xiaokaizip/debugger/README.assets/image-20221211133038720.png

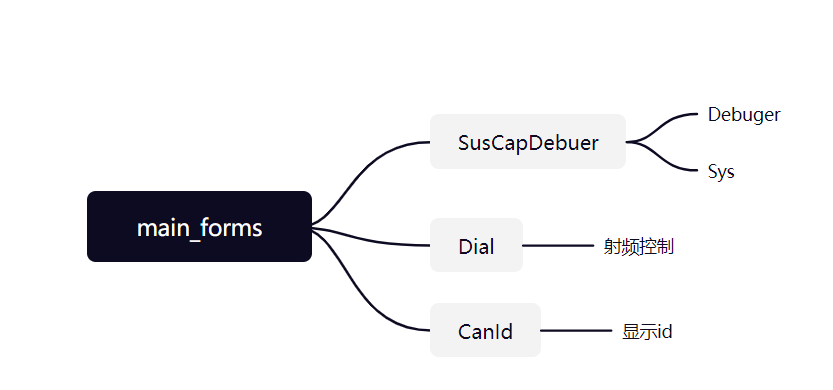
README.assets/image-20221211133038720.png
