xiaokaizip/debugger/debugger_code_f407/forms/motor_forms.h

//
// Created by 86136 on 2023/3/27.
//

#ifndef DEBUGGER_CODE_MOTOR_FORMS_H
#define DEBUGGER_CODE_MOTOR_FORMS_H

void Motor_Form_Init();

void Motor_Form_Load();

#endif //DEBUGGER_CODE_MOTOR_FORMS_H
