xiaokaizip/debugger/debugger_code_f103/hardwares/usart.c

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
/* Includes ------------------------------------------------------------------*/
#include "usart.h"

/* USER CODE BEGIN 0 */
#include "string.h"
#include "retarget.h"

extern uint16_t usart_times;
extern char usart_name[20];
extern uint8_t usart_data[8];

//串口中断的回调函数
void HAL_UART_RxCpltCallback(UART_HandleTypeDef *huart) {
    if (huart == &huart1) {
        strcpy(usart_name, "usart_typeC");
        usart_times = 0;
    } else if (huart == &huart4) {
        strcpy(usart_name, "usart_gh1.25");
        usart_times = 0;
    }
    HAL_UART_Receive_IT(&huart1, usart_data, 8);
    HAL_UART_Receive_IT(&huart4, usart_data, 8);
}

/* USER CODE END 0 */

UART_HandleTypeDef huart4;
UART_HandleTypeDef huart1;

/* UART4 init function */
void MX_UART4_Init(void) {

    huart4.Instance = UART4;
    huart4.Init.BaudRate = 115200;
    huart4.Init.WordLength = UART_WORDLENGTH_8B;
    huart4.Init.StopBits = UART_STOPBITS_1;
    huart4.Init.Parity = UART_PARITY_NONE;
    huart4.Init.Mode = UART_MODE_TX_RX;
    huart4.Init.HwFlowCtl = UART_HWCONTROL_NONE;
    huart4.Init.OverSampling = UART_OVERSAMPLING_16;
    if (HAL_UART_Init(&huart4) != HAL_OK) {
        Error_Handler();
    }
}

/* USART1 init function */

void MX_USART1_UART_Init(void) {

    huart1.Instance = USART1;
    huart1.Init.BaudRate = 115200;
    huart1.Init.WordLength = UART_WORDLENGTH_8B;
    huart1.Init.StopBits = UART_STOPBITS_1;
    huart1.Init.Parity = UART_PARITY_NONE;
    huart1.Init.Mode = UART_MODE_TX_RX;
    huart1.Init.HwFlowCtl = UART_HWCONTROL_NONE;
    huart1.Init.OverSampling = UART_OVERSAMPLING_16;
    if (HAL_UART_Init(&huart1) != HAL_OK) {
        Error_Handler();
    }
}

void HAL_UART_MspInit(UART_HandleTypeDef *uartHandle) {

    GPIO_InitTypeDef GPIO_InitStruct = {0};
    if (uartHandle->Instance == UART4) {
        /* UART4 clock enable */
        __HAL_RCC_UART4_CLK_ENABLE();

        __HAL_RCC_GPIOC_CLK_ENABLE();
        /**UART4 GPIO Configuration
        PC10     ------> UART4_TX
        PC11     ------> UART4_RX
        */
        GPIO_InitStruct.Pin = GPIO_PIN_10;
        GPIO_InitStruct.Mode = GPIO_MODE_AF_PP;
        GPIO_InitStruct.Speed = GPIO_SPEED_FREQ_HIGH;
        HAL_GPIO_Init(GPIOC, &GPIO_InitStruct);

        GPIO_InitStruct.Pin = GPIO_PIN_11;
        GPIO_InitStruct.Mode = GPIO_MODE_INPUT;
        GPIO_InitStruct.Pull = GPIO_NOPULL;
        HAL_GPIO_Init(GPIOC, &GPIO_InitStruct);

        /* UART4 interrupt Init */
        HAL_NVIC_SetPriority(UART4_IRQn, 0, 0);
        HAL_NVIC_EnableIRQ(UART4_IRQn);
    } else if (uartHandle->Instance == USART1) {
        /* USART1 clock enable */
        __HAL_RCC_USART1_CLK_ENABLE();

        __HAL_RCC_GPIOA_CLK_ENABLE();
        /**USART1 GPIO Configuration
        PA9     ------> USART1_TX
        PA10     ------> USART1_RX
        */
        GPIO_InitStruct.Pin = GPIO_PIN_9;
        GPIO_InitStruct.Mode = GPIO_MODE_AF_PP;
        GPIO_InitStruct.Speed = GPIO_SPEED_FREQ_HIGH;
        HAL_GPIO_Init(GPIOA, &GPIO_InitStruct);

        GPIO_InitStruct.Pin = GPIO_PIN_10;
        GPIO_InitStruct.Mode = GPIO_MODE_INPUT;
        GPIO_InitStruct.Pull = GPIO_NOPULL;
        HAL_GPIO_Init(GPIOA, &GPIO_InitStruct);

        /* USART1 interrupt Init */
        HAL_NVIC_SetPriority(USART1_IRQn, 0, 0);
        HAL_NVIC_EnableIRQ(USART1_IRQn);
    }
}

void HAL_UART_MspDeInit(UART_HandleTypeDef *uartHandle) {

    if (uartHandle->Instance == UART4) {
        /* Peripheral clock disable */
        __HAL_RCC_UART4_CLK_DISABLE();

        /**UART4 GPIO Configuration
        PC10     ------> UART4_TX
        PC11     ------> UART4_RX
        */
        HAL_GPIO_DeInit(GPIOC, GPIO_PIN_10 | GPIO_PIN_11);

        /* UART4 interrupt Deinit */
        HAL_NVIC_DisableIRQ(UART4_IRQn);
    } else if (uartHandle->Instance == USART1) {
        /* Peripheral clock disable */
        __HAL_RCC_USART1_CLK_DISABLE();

        /**USART1 GPIO Configuration
        PA9     ------> USART1_TX
        PA10     ------> USART1_RX
        */
        HAL_GPIO_DeInit(GPIOA, GPIO_PIN_9 | GPIO_PIN_10);

        /* USART1 interrupt Deinit */
        HAL_NVIC_DisableIRQ(USART1_IRQn);
    }
}
