xiaokaizip/debugger/debugger_code_f103/system/system.h

//
// Created by 86136 on 2023/1/15.
//

#ifndef DEBUGGER_CODE_SYSTEM_H
#define DEBUGGER_CODE_SYSTEM_H

unsigned short FloatToInt16(float data0);

float Int16ToFloat(unsigned short data0);

#endif //DEBUGGER_CODE_SYSTEM_H
