xiaokaizip/debugger/debugger_code_f407/function/led.c

/*

The MIT License (MIT)

Copyright (c) 2016 Hubert Denkmair

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
*/

#include "led.h"
#include <string.h>
#include "main.h"

#define SEQ_ISPASSED(now, target) ((int32_t) ((now) - (target)) >= 0)   /*判断大小*/

/**
 * 初始化led灯
 * @param leds led的结构体
 * @param led1_port LED1引脚所在的组
 * @param led1_pin  LED1的引脚号
 * @param led1_active_high
 * @param led2_port LED2引脚所在的组
 * @param led2_pin  LED2的引脚号
 * @param led2_active_high
 */
void led_init(
        led_data_t *leds,
        void *led1_port, uint16_t led1_pin, bool led1_active_high,
        void *led2_port, uint16_t led2_pin, bool led2_active_high
) {
    memset(leds, 0, sizeof(led_data_t));
    leds->led_state[0].port = led1_port;
    leds->led_state[0].pin = led1_pin;
    leds->led_state[0].is_active_high = led1_active_high;
    leds->led_state[1].port = led2_port;
    leds->led_state[1].pin = led2_pin;
    leds->led_state[1].is_active_high = led2_active_high;
}

/**
 * 设置led灯的模式
 * @param leds  leds的结构体
 * @param mode  模式：有	led_mode_off,led_mode_normal,led_mode_warn,led_mode_error,led_mode_sequence五种
 */
void led_set_mode(led_data_t *leds, led_mode_t mode) {
    leds->mode = mode;
    led_update(leds);
}

/**
 * 设置led灯的状态
 * @param led
 * @param state
 */
static void led_set(led_state_t *led, bool state) {
    if (!led->is_active_high) {
        state = !state;
    }
    HAL_GPIO_WritePin(led->port, led->pin, state ? GPIO_PIN_SET : GPIO_PIN_RESET);
}

static uint32_t led_set_sequence_step(led_data_t *leds, uint32_t step_num) {
    led_seq_step_t *step = &leds->sequence[step_num];
    leds->sequence_step = step_num;
    led_set(&leds->led_state[0], step->state & 0x01);
    led_set(&leds->led_state[1], step->state & 0x02);
    uint32_t delta = 10 * step->time_in_10ms;
    if (delta > INT32_MAX) {
        delta = INT32_MAX;    //clamp
    }
    leds->t_sequence_next = HAL_GetTick() + delta;
    return delta;
}

void led_run_sequence(led_data_t *leds, led_seq_step_t *sequence, int32_t num_repeat) {
    leds->last_mode = leds->mode;
    leds->mode = led_mode_sequence;
    leds->sequence = sequence;
    leds->seq_num_repeat = num_repeat;
    led_set_sequence_step(leds, 0);
    led_update(leds);
}

void led_indicate_trx(led_data_t *leds, led_num_t num) {
    uint32_t now = HAL_GetTick();
    led_state_t *led = &leds->led_state[num];

    if (SEQ_ISPASSED(now, led->on_until) &&
        SEQ_ISPASSED(now, led->off_until)) {
        led->off_until = now + 30;
        led->on_until = now + 45;
    }

    led_update(leds);
}

static void led_update_normal_mode(led_state_t *led) {
    uint32_t now = HAL_GetTick();
    led_set(led, SEQ_ISPASSED(now, led->off_until));
}

static void led_update_sequence(led_data_t *leds) {
    if (leds->sequence == NULL) {
        return;
    }

    uint32_t now = HAL_GetTick();
    if (SEQ_ISPASSED(now, leds->t_sequence_next)) {

        uint32_t t = led_set_sequence_step(leds, ++leds->sequence_step);

        if (t > 0) { // the saga continues

            leds->t_sequence_next = now + t;

        } else { // end of sequence

            if (leds->seq_num_repeat != 0) {

                if (leds->seq_num_repeat > 0) {
                    leds->seq_num_repeat--;
                }

                led_set_sequence_step(leds, 0);

            } else {
                leds->sequence = NULL;
            }
        }
    }
}

/**
 * 更新led结构体的模式。
 * @param leds
 */
void led_update(led_data_t *leds) {
    switch (leds->mode) {

        case led_mode_off:
            //关闭两个led灯
            led_set(&leds->led_state[0], false);
            led_set(&leds->led_state[1], false);
            break;

        case led_mode_normal:
            //更新两个led的状态
            led_update_normal_mode(&leds->led_state[0]);
            led_update_normal_mode(&leds->led_state[1]);
            break;

        case led_mode_sequence:
            led_update_sequence(leds);
            break;

        default:
            led_set(&leds->led_state[0], false);
            led_set(&leds->led_state[1], true);
    }
}
