xiaokaizip/debugger/debugger_code_f407/data_processing/can_data.c

//
// Created by 86136 on 2023/5/21.
//

#include "can_data.h"
#include "usart.h"

void fifo_can_motor(fifo_s_t *can_fifo_motor, moto_measure_t motor_measure[8]) {
    can_data_t can_data;

    if (fifo_s_used(can_fifo_motor)) {
        fifo_s_gets(can_fifo_motor, (char *) &can_data, sizeof(can_data_t));
        if (can_data.id >= 0x201 && can_data.id <= 0x208) {
            int i = can_data.id - 0x201;
            get_moto_measure(&motor_measure[i], can_data.data);
        }
    }
}

void fifo_can_IMU(fifo_s_t *can_fifo_IMU, IMU_measure_t *IMU_measure) {
    can_data_t can_data;
    if (fifo_s_used(can_fifo_IMU)) {
        fifo_s_gets(can_fifo_IMU, (char *) &can_data, sizeof(can_data_t));
        if (can_data.id == 0x101 || can_data.id <= 0x100) {
            get_BIM1088_data(IMU_measure, can_data.data, can_data.id);
        }
    }
}
