xiaokaizip/debugger/debugger_code_f407/forms/logic_forms.c

//
// Created by 86136 on 2022/12/9.
//

#include "main.h"

extern Forms_struct_t forms;

void Form_UpdateEvent(void) {

    switch (forms.id) {
        case Main_Form:
            main_Form_Load();
            break;
        case SusCapDebuger:
            Suscap_Debuger_Show_Load();
            break;
        case Dail:
            Dail_Form_Load();
            break;
        case CanId:
            CanId_Form_Load();
            break;
        case Usart:
            Usart_Form_Load();
            break;
        case Imu:
            Imu_Form_Load();
            break;
        case Motor:
            Motor_Form_Load();
            break;
        default:
            main_Form_Load();
            break;
    }
}
