xiaokaizip/debugger/debugger_code_f407/forms/usart_forms.h

//
// Created by 86136 on 2023/1/13.
//

#ifndef DEBUGGER_CODE_USART_FORMS_H
#define DEBUGGER_CODE_USART_FORMS_H


void Usart_Form_Init();

void Usart_Form_Load();

#endif //DEBUGGER_CODE_USART_FORMS_H
