xiaokaizip/debugger/debugger_code_f407/forms/canid_forms.h

//
// Created by 86136 on 2022/12/11.
//

#ifndef DEBUGGER_CODE_CANID_FORMS_H
#define DEBUGGER_CODE_CANID_FORMS_H

void CanId_Form_Init();

void CanId_Form_Load();

#endif //DEBUGGER_CODE_CANID_FORMS_H
