xiaokaizip/debugger/debugger_code_f407/forms/suscap_debuger_forms.h

//
// Created by 86136 on 2022/12/2.
//

#ifndef DEBUGGER_CODE_SUSCAP_DEBUGER_FORMS_H
#define DEBUGGER_CODE_SUSCAP_DEBUGER_FORMS_H

void Suscap_Debuger_Show_Init();

void Suscap_Debuger_Show_Load();

#endif //DEBUGGER_CODE_SUSCAP_DEBUGER_FORMS_H
